AndrejChoo/USB-Programmer-parallel-flash-and-eeprom/hardware/AUTO_DCDC_MODIFICATION/AutoDCDC_MOD.jpg

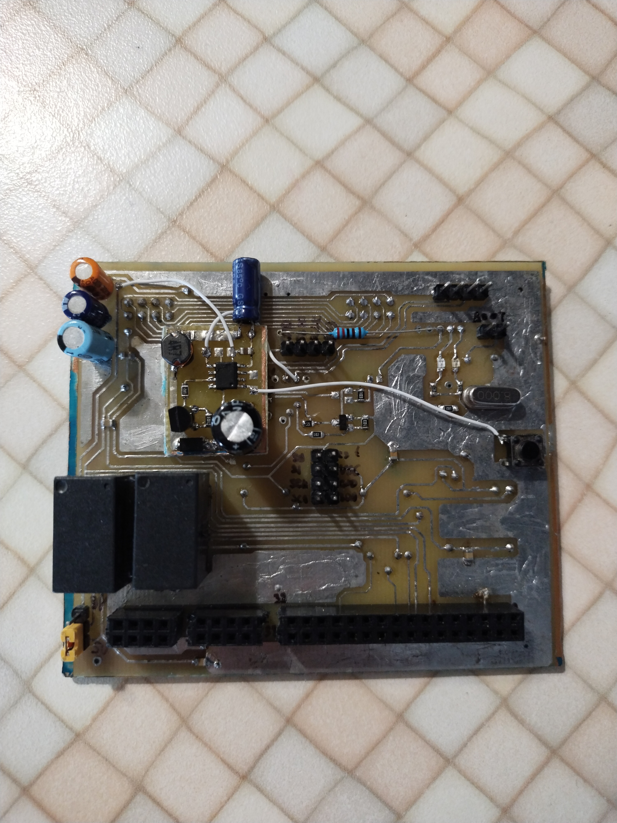
hardware/AUTO_DCDC_MODIFICATION/AutoDCDC_MOD.jpg
