AndrejChoo/USB-Programmer-parallel-flash-and-eeprom/hardware/AUTO_DCDC_MODIFICATION/PRG_SETTINGS.png

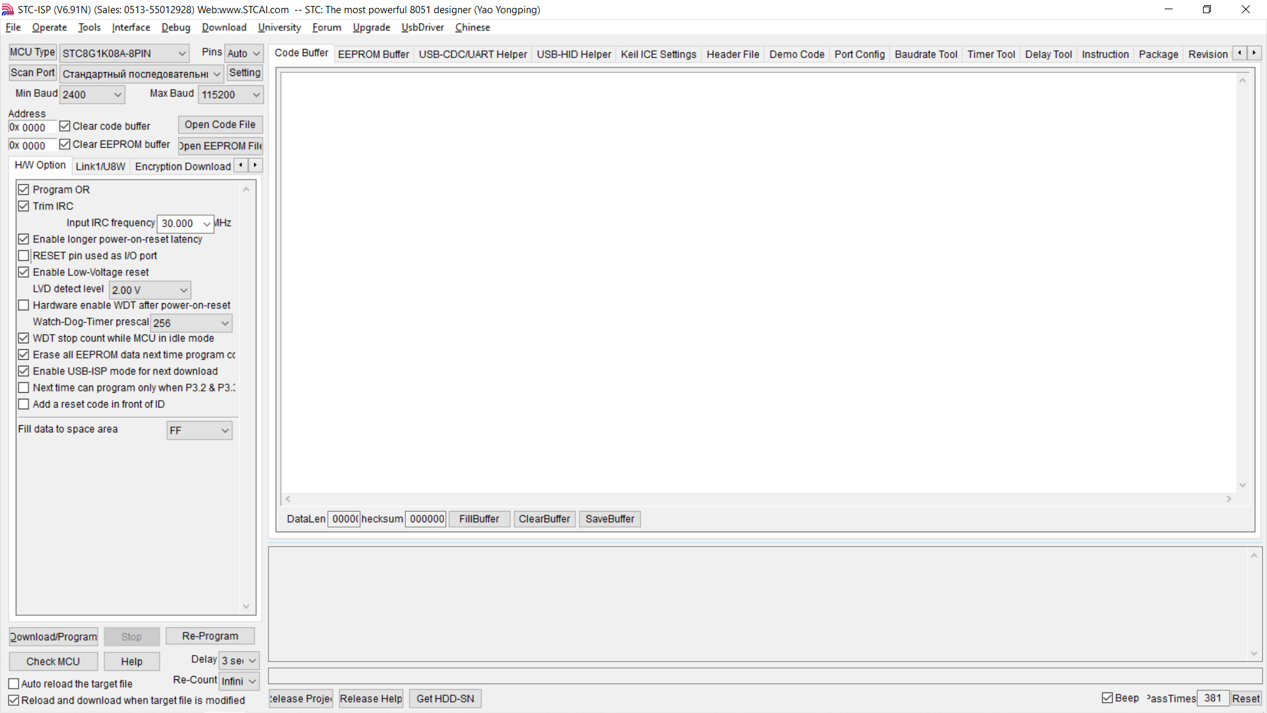
hardware/AUTO_DCDC_MODIFICATION/PRG_SETTINGS.png
