AndrejChoo/USB-Programmer-parallel-flash-and-eeprom/hardware/AUTO_DCDC_MODIFICATION/Schematic_AutoDCDC.png

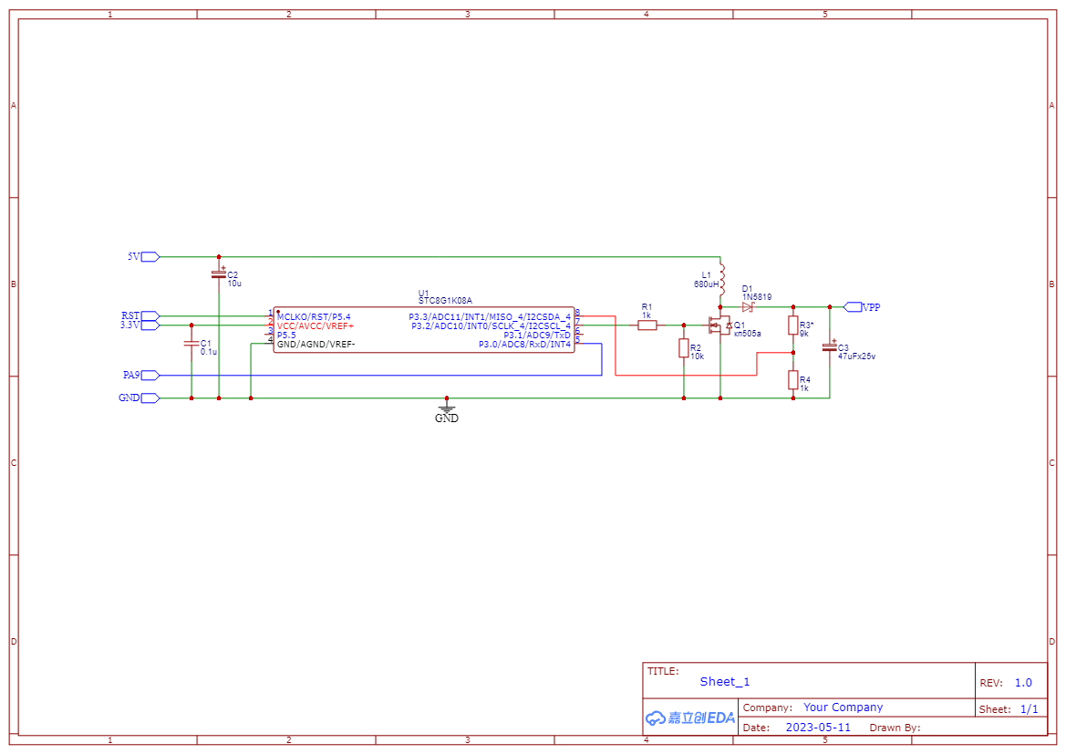
hardware/AUTO_DCDC_MODIFICATION/Schematic_AutoDCDC.png
