AndrejChoo/USB-Programmer-parallel-flash-and-eeprom/hardware/Case_model/case.jpg

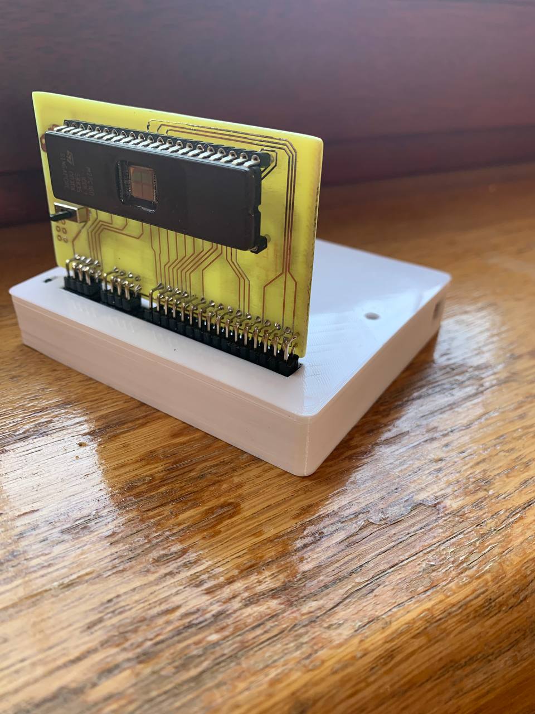
hardware/Case_model/case.jpg
