AndrejChoo/USB-Programmer-parallel-flash-and-eeprom/hardware/images/ParallelProg_v2_1_Up.jpg

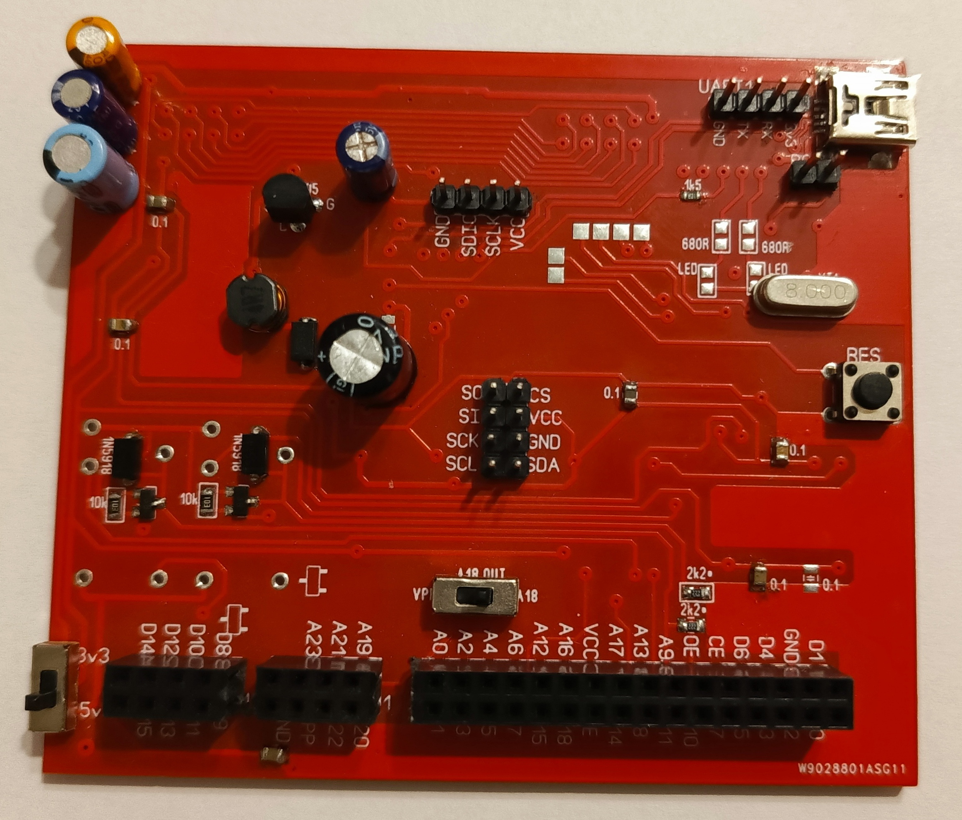
hardware/images/ParallelProg_v2_1_Up.jpg
