AndrejChoo/USB-Programmer-parallel-flash-and-eeprom/hardware/NO_RELAY_MOD/PCB_V2_NO_RELAY_PCBWAY.jpg

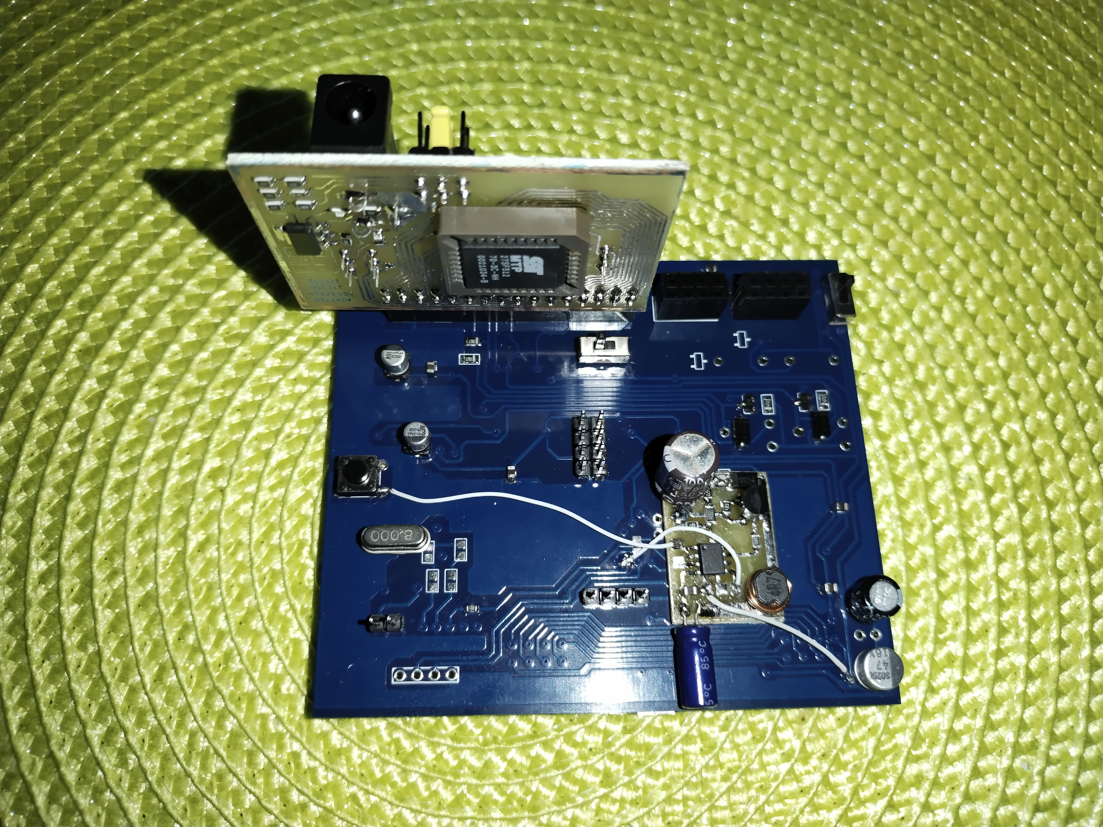
hardware/NO_RELAY_MOD/PCB_V2_NO_RELAY_PCBWAY.jpg
