AndrejChoo/USB-Programmer-parallel-flash-and-eeprom/hardware/NO_RELAY_MOD/Schematic_HV_KEY_2023-05-28.png

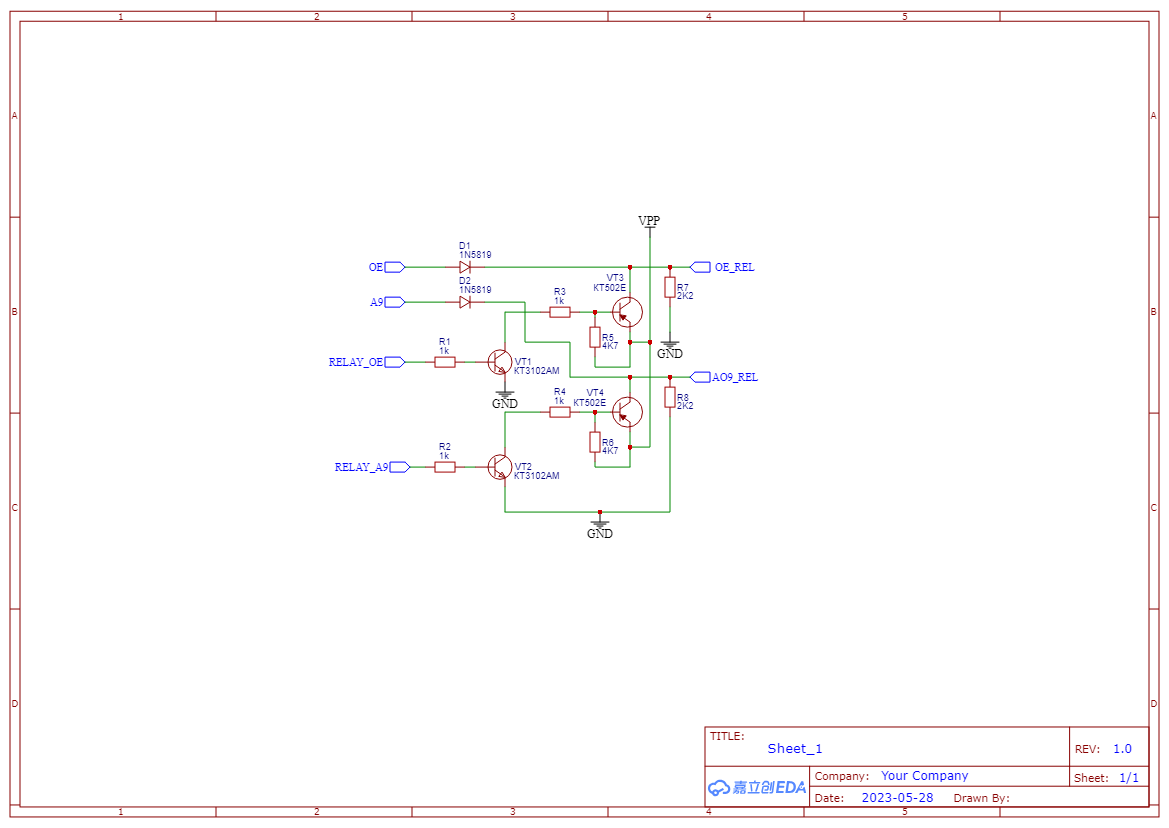
hardware/NO_RELAY_MOD/Schematic_HV_KEY_2023-05-28.png
