AndrejChoo/USB-Programmer-parallel-flash-and-eeprom/hardware/pcb/adapters/AVR/atmega_8_DIP28_Down.jpg

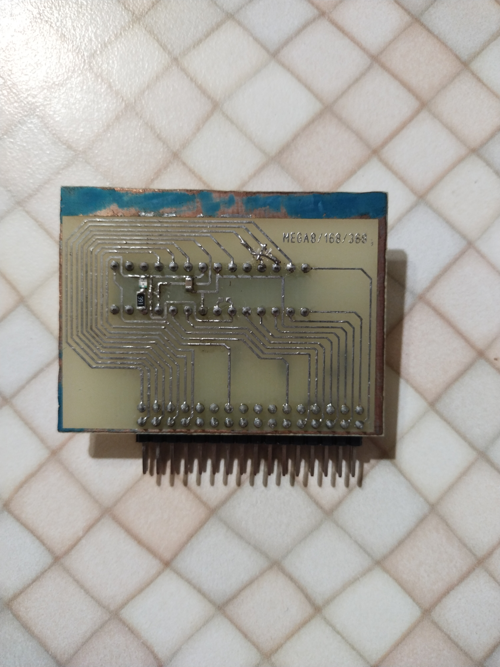
hardware/pcb/adapters/AVR/atmega_8_DIP28_Down.jpg
