AndrejChoo/USB-Programmer-parallel-flash-and-eeprom/hardware/pcb/adapters/AVR/atmega_8_DIP28_UP.jpg

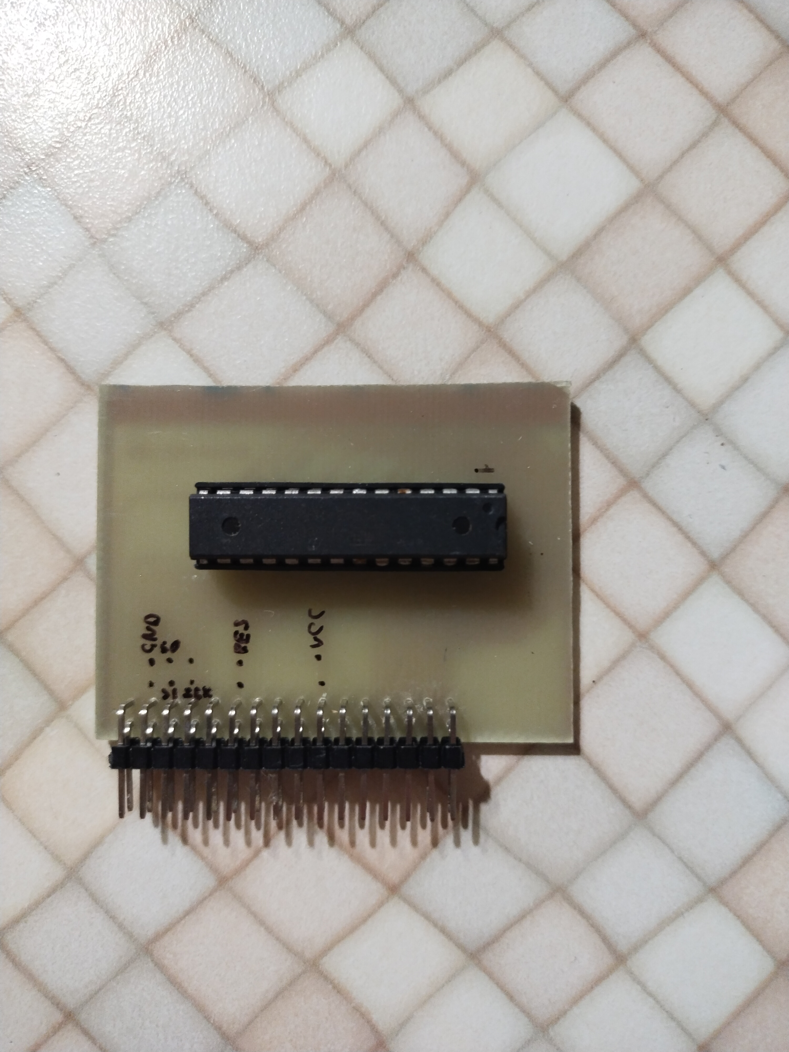
hardware/pcb/adapters/AVR/atmega_8_DIP28_UP.jpg
