AndrejChoo/USB-Programmer-parallel-flash-and-eeprom/hardware/pcb/adapters/AVR/atmega_16_DIP40_UP.jpg

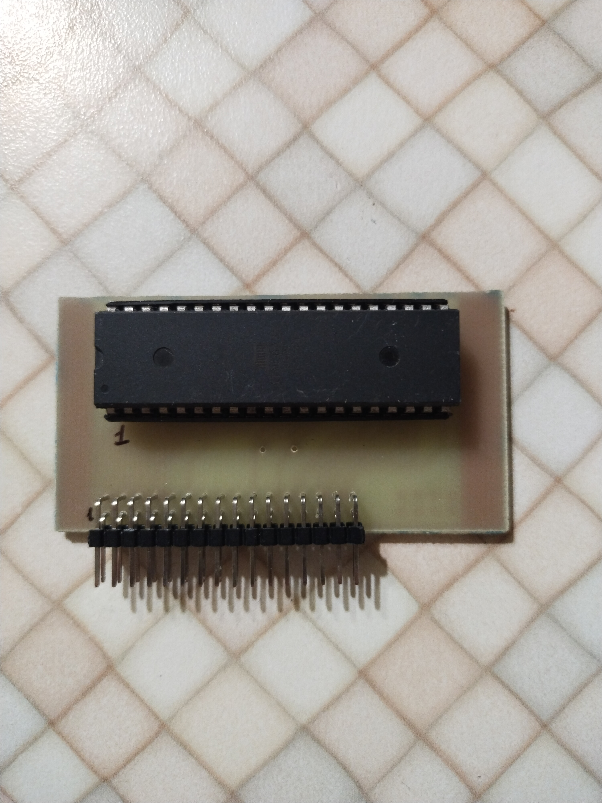
hardware/pcb/adapters/AVR/atmega_16_DIP40_UP.jpg
