AndrejChoo/USB-Programmer-parallel-flash-and-eeprom/hardware/pcb/adapters/AVR/atmega_16_DIP_40_DOWN.jpg

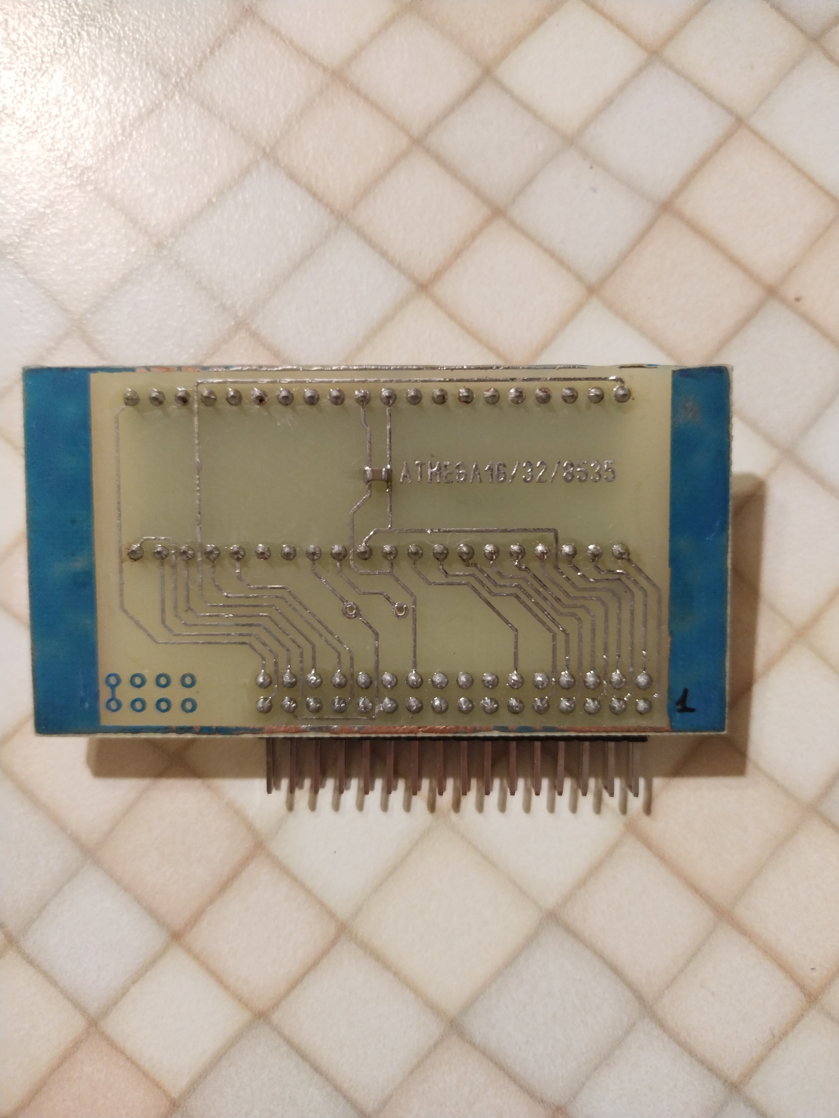
hardware/pcb/adapters/AVR/atmega_16_DIP_40_DOWN.jpg
