AndrejChoo/USB-Programmer-parallel-flash-and-eeprom/hardware/pcb/adapters/AVR/attiny_x5_UP.jpg

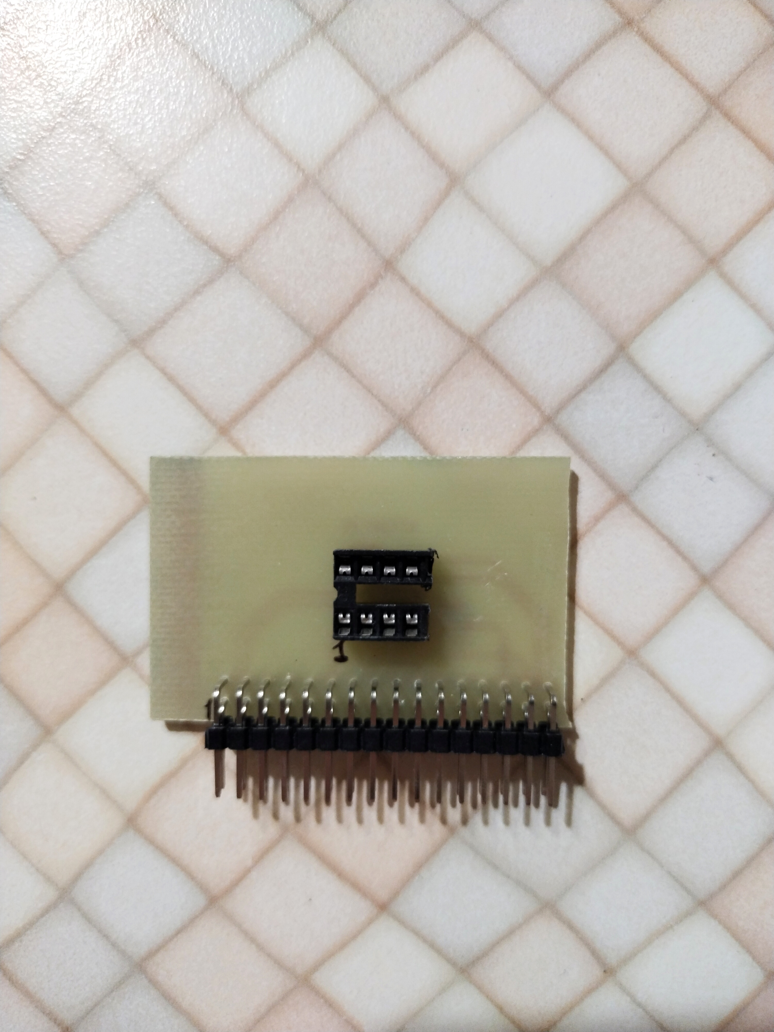
hardware/pcb/adapters/AVR/attiny_x5_UP.jpg
