AndrejChoo/USB-Programmer-parallel-flash-and-eeprom/hardware/pcb/adapters/AVR/attinyx313_DOWN.jpg

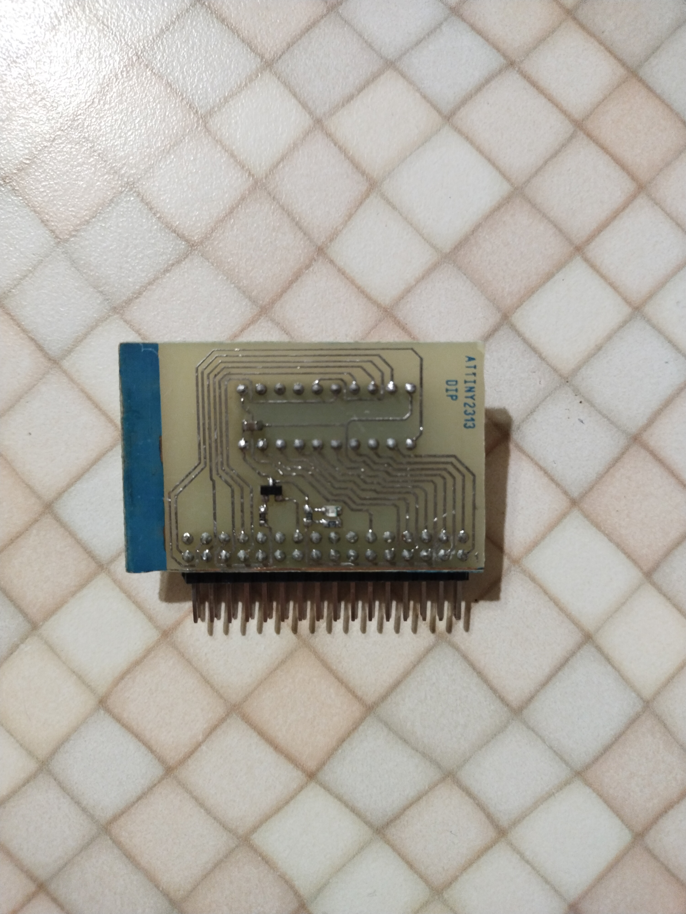
hardware/pcb/adapters/AVR/attinyx313_DOWN.jpg
