AndrejChoo/USB-Programmer-parallel-flash-and-eeprom/hardware/pcb/adapters/AVR/attynyx313_UP.jpg

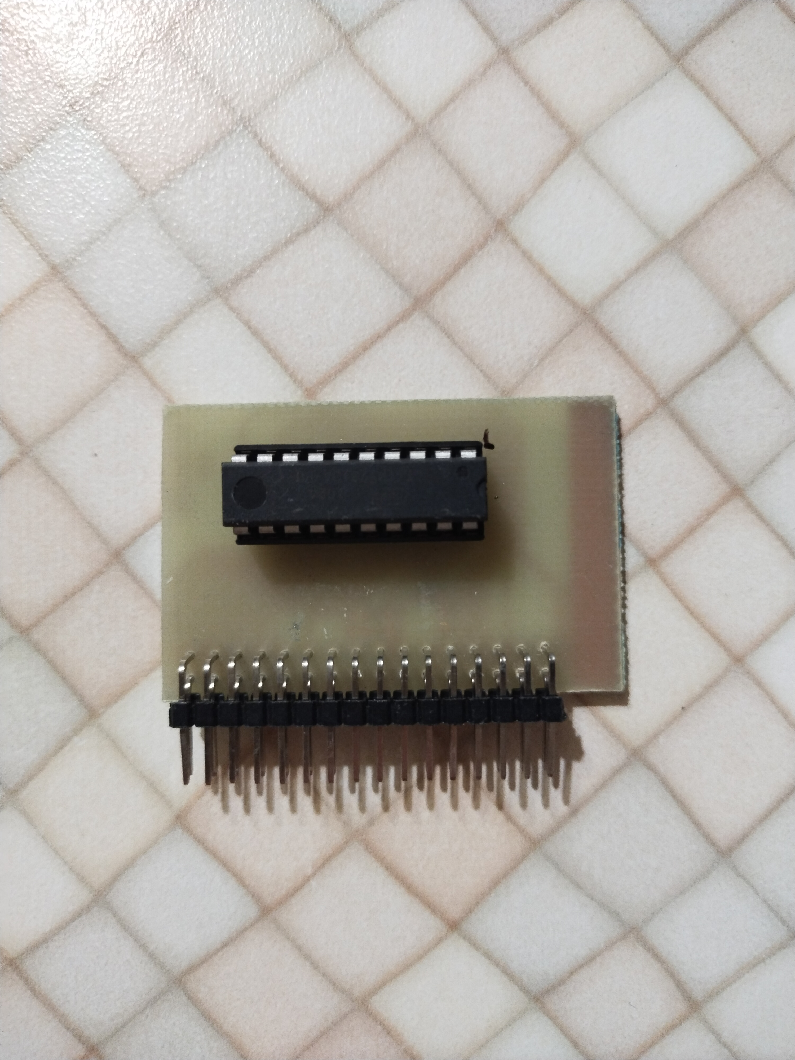
hardware/pcb/adapters/AVR/attynyx313_UP.jpg
