AndrejChoo/USB-Programmer-parallel-flash-and-eeprom/hardware/pcb/adapters/AVR/PLCC32_atmega_socket1.jpg

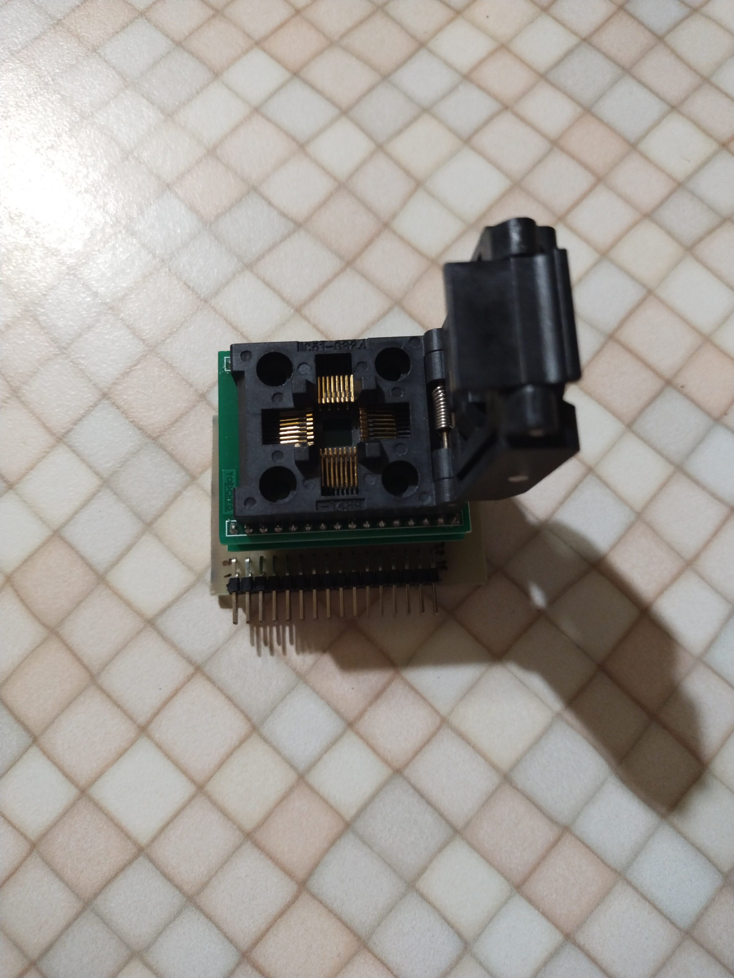
hardware/pcb/adapters/AVR/PLCC32_atmega_socket1.jpg
