AndrejChoo/USB-Programmer-parallel-flash-and-eeprom/hardware/pcb/adapters/AVR/PLCC32_atmega_socket2.jpg

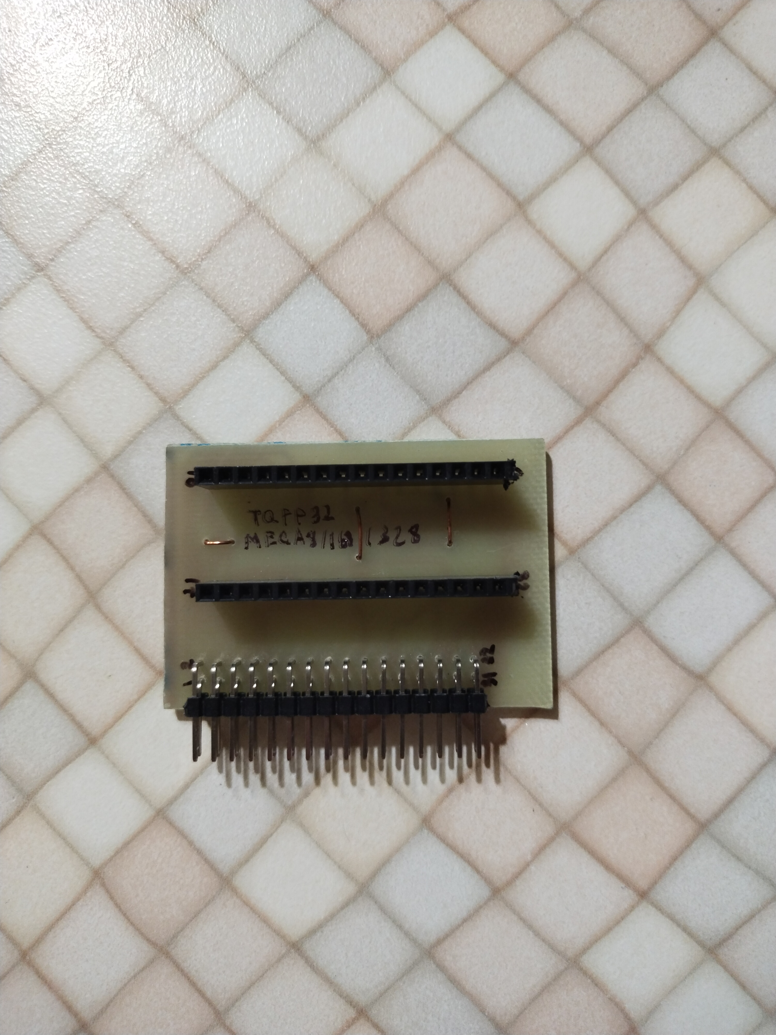
hardware/pcb/adapters/AVR/PLCC32_atmega_socket2.jpg
