AndrejChoo/USB-Programmer-parallel-flash-and-eeprom/hardware/pcb/adapters/DIP32/DOWN.jpg

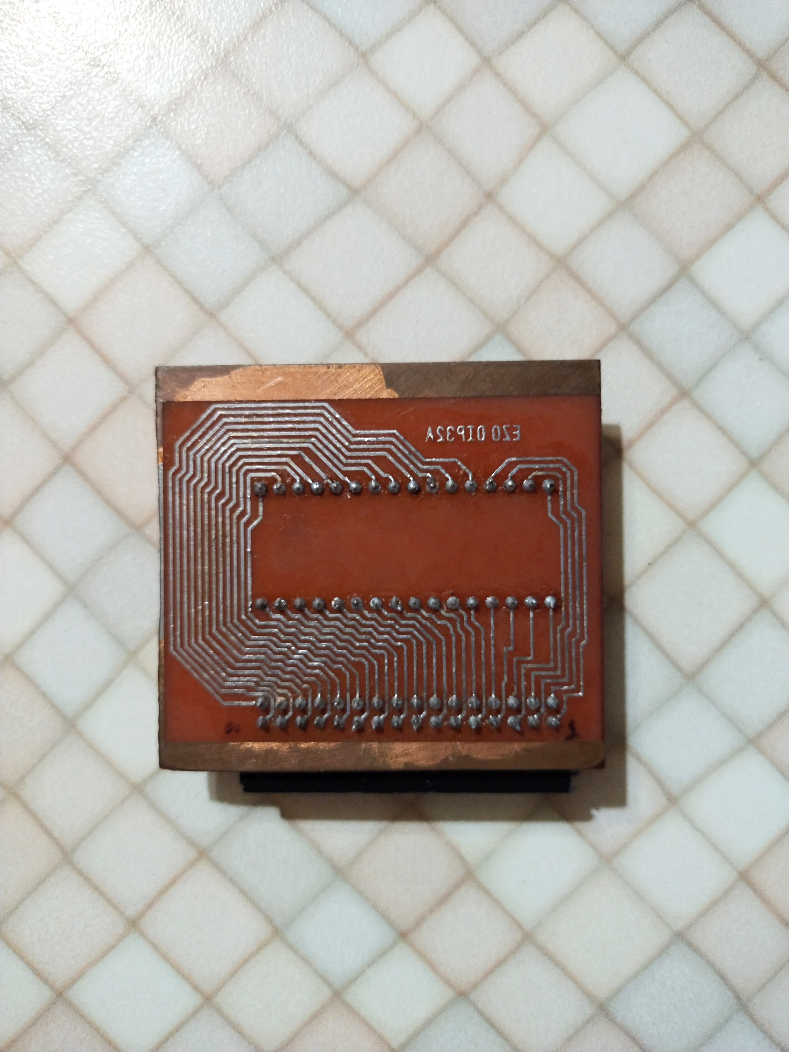
hardware/pcb/adapters/DIP32/DOWN.jpg
