AndrejChoo/USB-Programmer-parallel-flash-and-eeprom/hardware/pcb/adapters/DIP32/UP.jpg

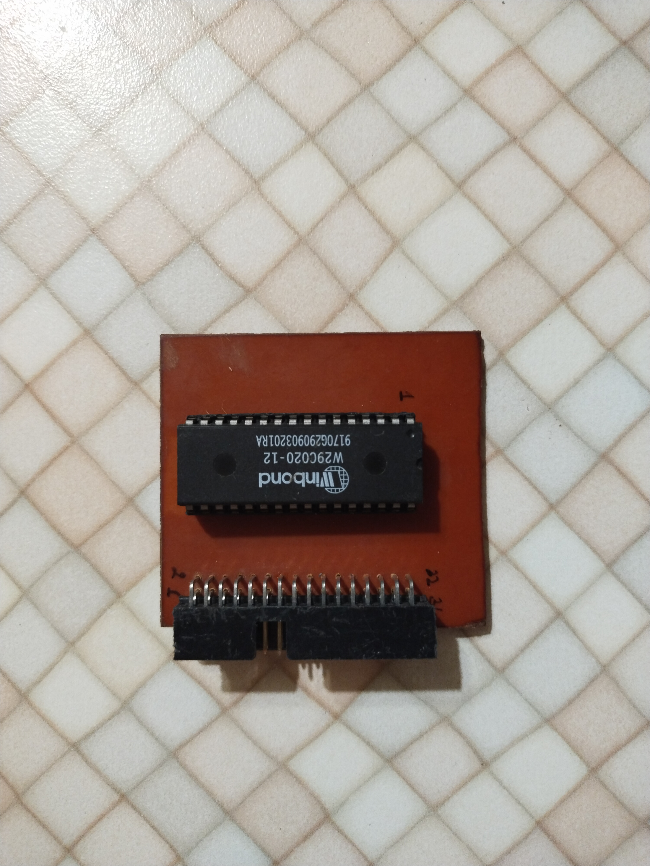
hardware/pcb/adapters/DIP32/UP.jpg
