AndrejChoo/USB-Programmer-parallel-flash-and-eeprom/hardware/pcb/adapters/EPROM_27C256_27C512/PLCC32_DOWN.jpg

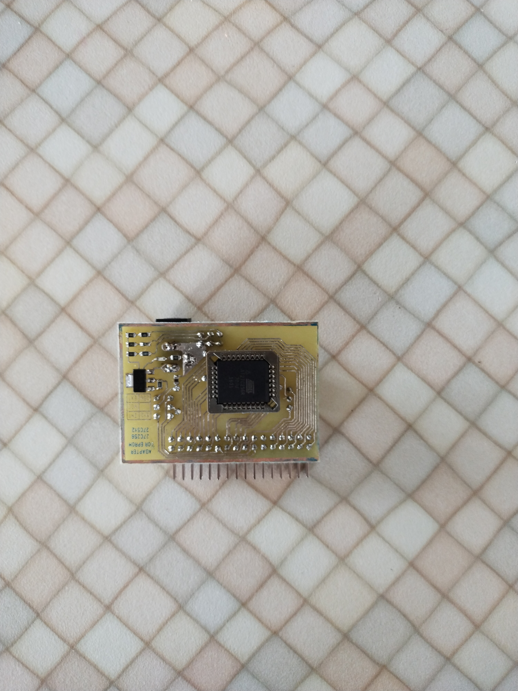
hardware/pcb/adapters/EPROM_27C256_27C512/PLCC32_DOWN.jpg
