AndrejChoo/USB-Programmer-parallel-flash-and-eeprom/hardware/pcb/adapters/EPROM_27C256_27C512/PLCC32_UP.jpg

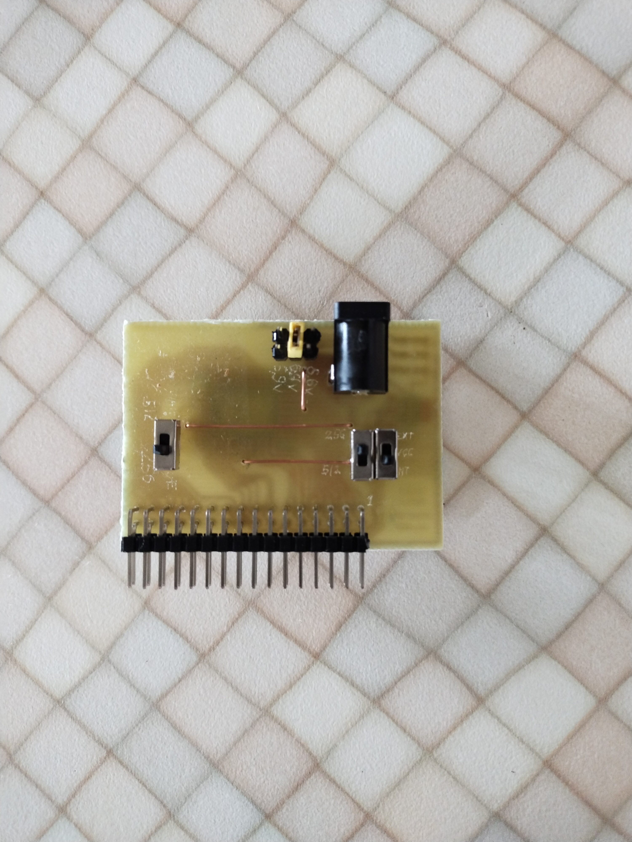
hardware/pcb/adapters/EPROM_27C256_27C512/PLCC32_UP.jpg
