AndrejChoo/USB-Programmer-parallel-flash-and-eeprom/hardware/pcb/adapters/PLCC32_HUB_FLASH/IMG_20230411_193900.jpg

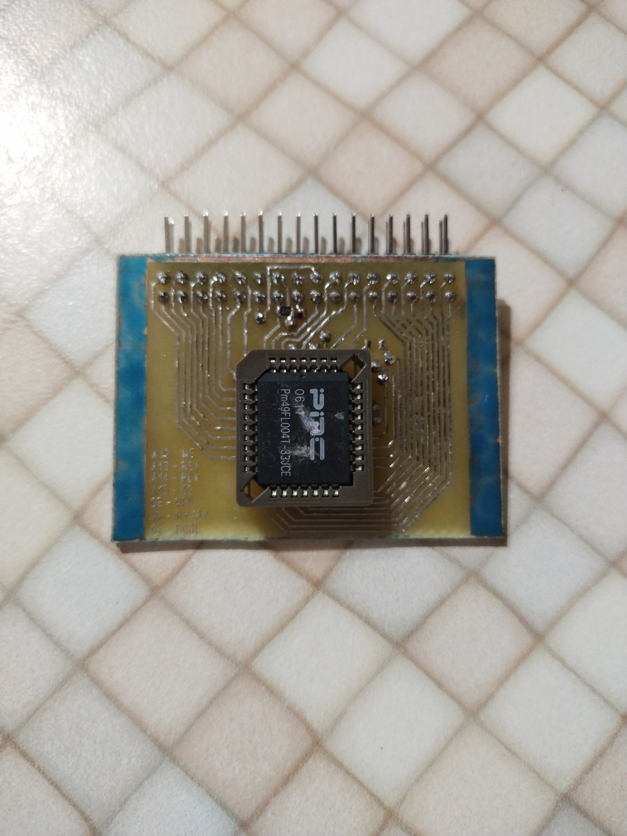
hardware/pcb/adapters/PLCC32_HUB_FLASH/IMG_20230411_193900.jpg
