AndrejChoo/USB-Programmer-parallel-flash-and-eeprom/hardware/pcb/adapters/SO28/SO28_SOCK_DOWN.jpg

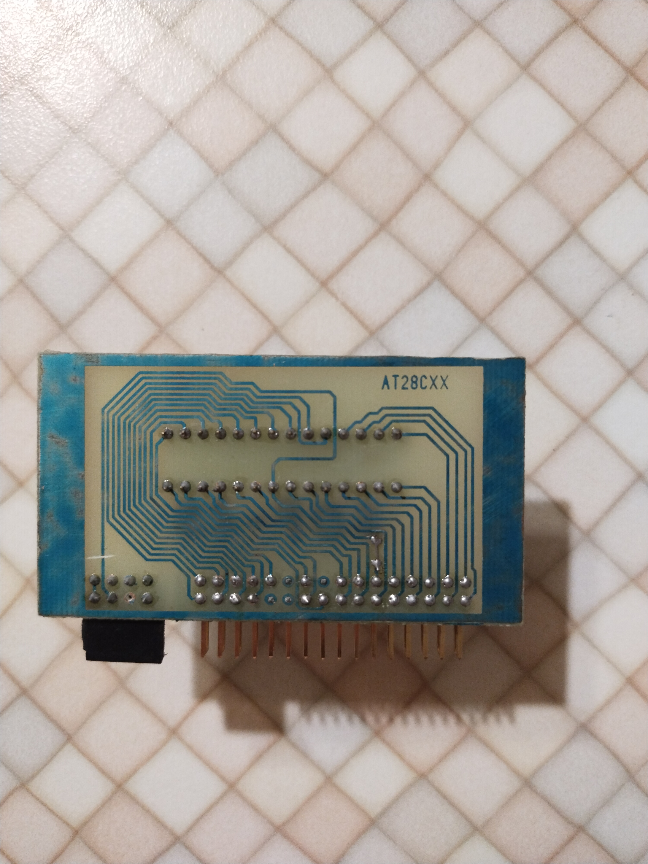
hardware/pcb/adapters/SO28/SO28_SOCK_DOWN.jpg
