AndrejChoo/USB-Programmer-parallel-flash-and-eeprom/hardware/pcb/adapters/SO28/SO28_SOCK_UP1.jpg

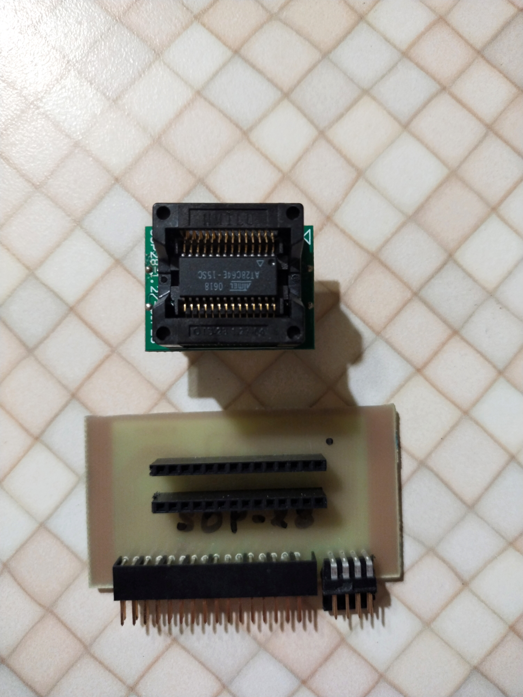
hardware/pcb/adapters/SO28/SO28_SOCK_UP1.jpg
