AndrejChoo/USB-Programmer-parallel-flash-and-eeprom/hardware/pcb/adapters/SO28/SO28_SOCK_UP.jpg

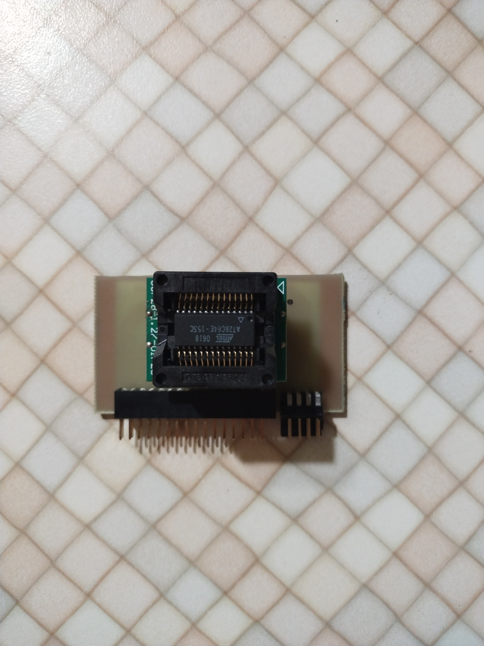
hardware/pcb/adapters/SO28/SO28_SOCK_UP.jpg
