AndrejChoo/USB-Programmer-parallel-flash-and-eeprom/hardware/pcb/adapters/TSOP32/DOWN.jpg

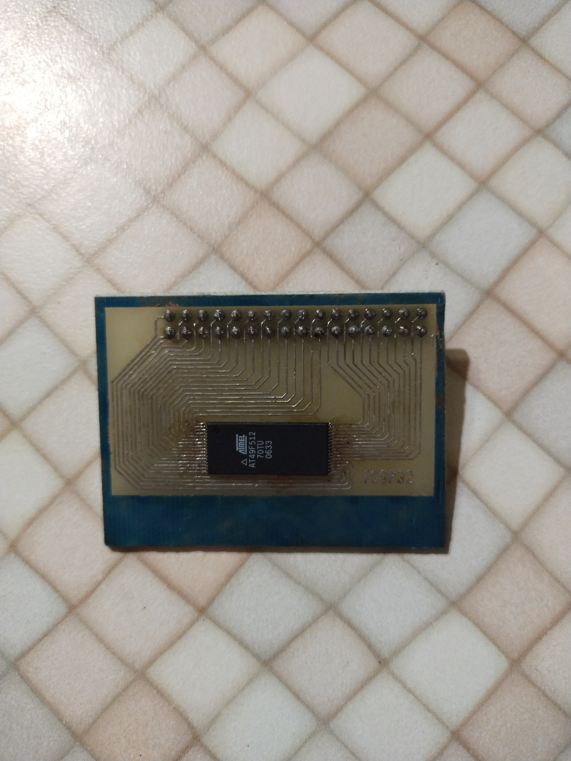
hardware/pcb/adapters/TSOP32/DOWN.jpg
