AndrejChoo/USB-Programmer-parallel-flash-and-eeprom/hardware/pcb/adapters/TSOP48_16Bit/IMG_20230411_193925.jpg

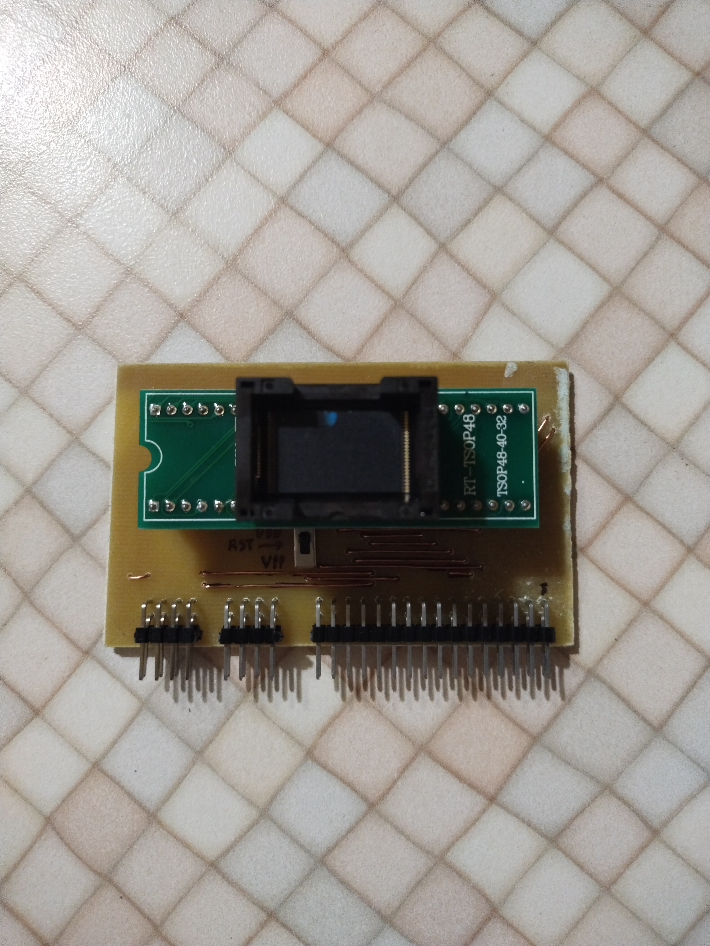
hardware/pcb/adapters/TSOP48_16Bit/IMG_20230411_193925.jpg
