AndrejChoo/USB-Programmer-parallel-flash-and-eeprom/hardware/pcb/adapters/TSOP48_16Bit/Kolodka.png

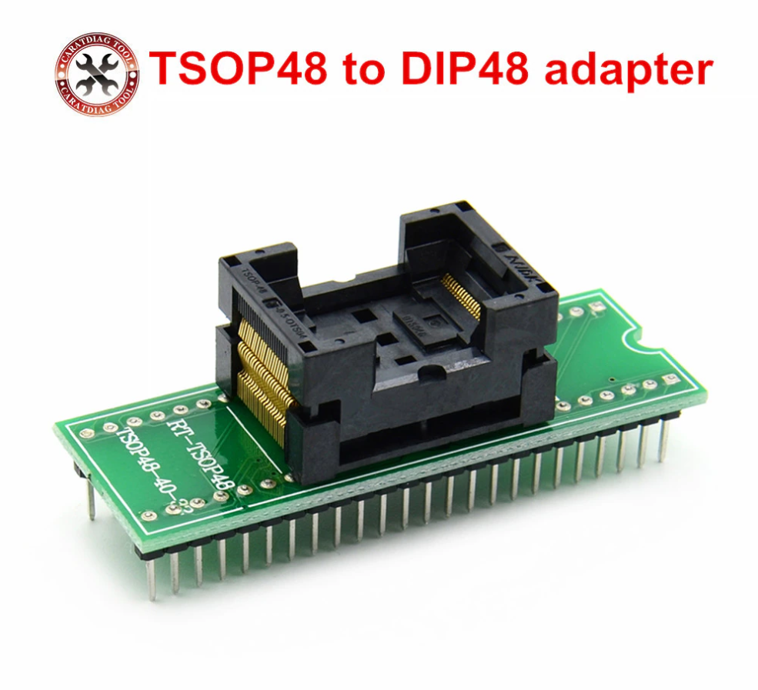
hardware/pcb/adapters/TSOP48_16Bit/Kolodka.png
