AndrejChoo/USB-Programmer-parallel-flash-and-eeprom/hardware/pcb/adapters/TSOP48_16Bit/Schematic_Flash_16b_adapter_2024-04-20.png

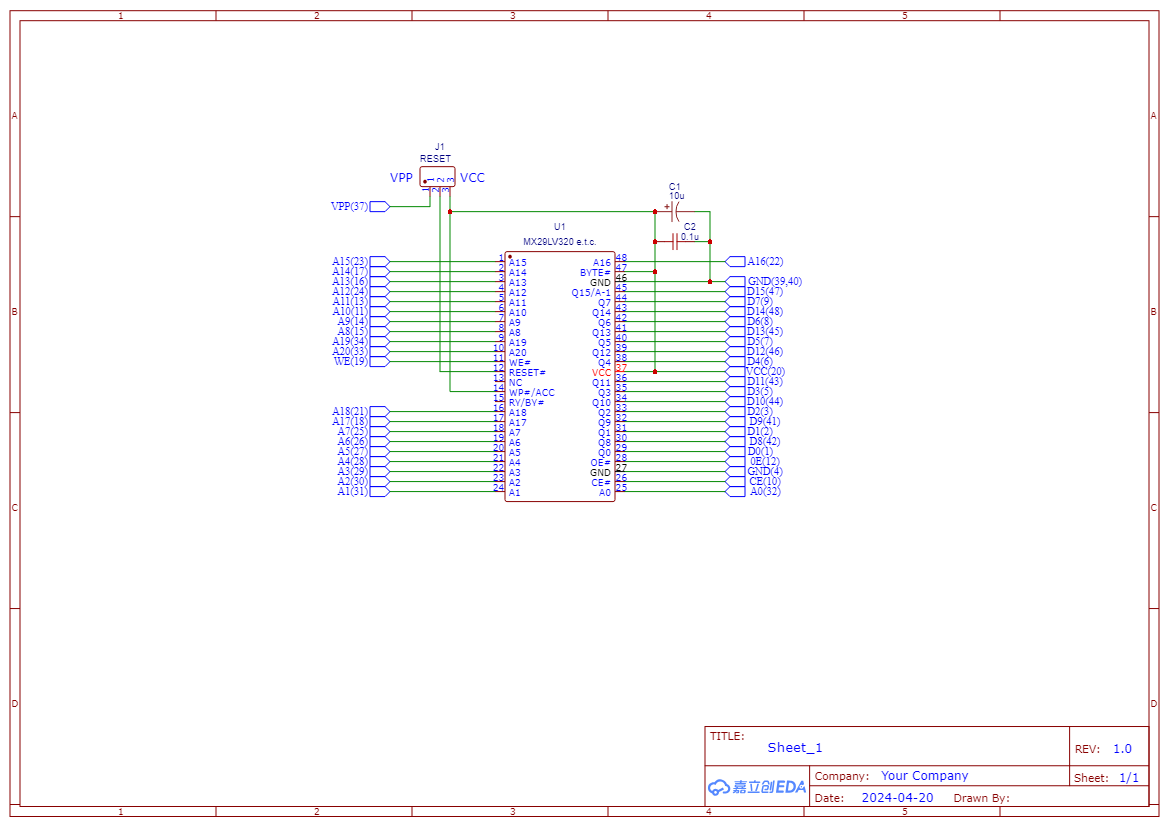
hardware/pcb/adapters/TSOP48_16Bit/Schematic_Flash_16b_adapter_2024-04-20.png
