AndrejChoo/USB-Programmer-parallel-flash-and-eeprom/hardware/AUTO_DCDC_MODIFICATION/MOD_Instruct.png

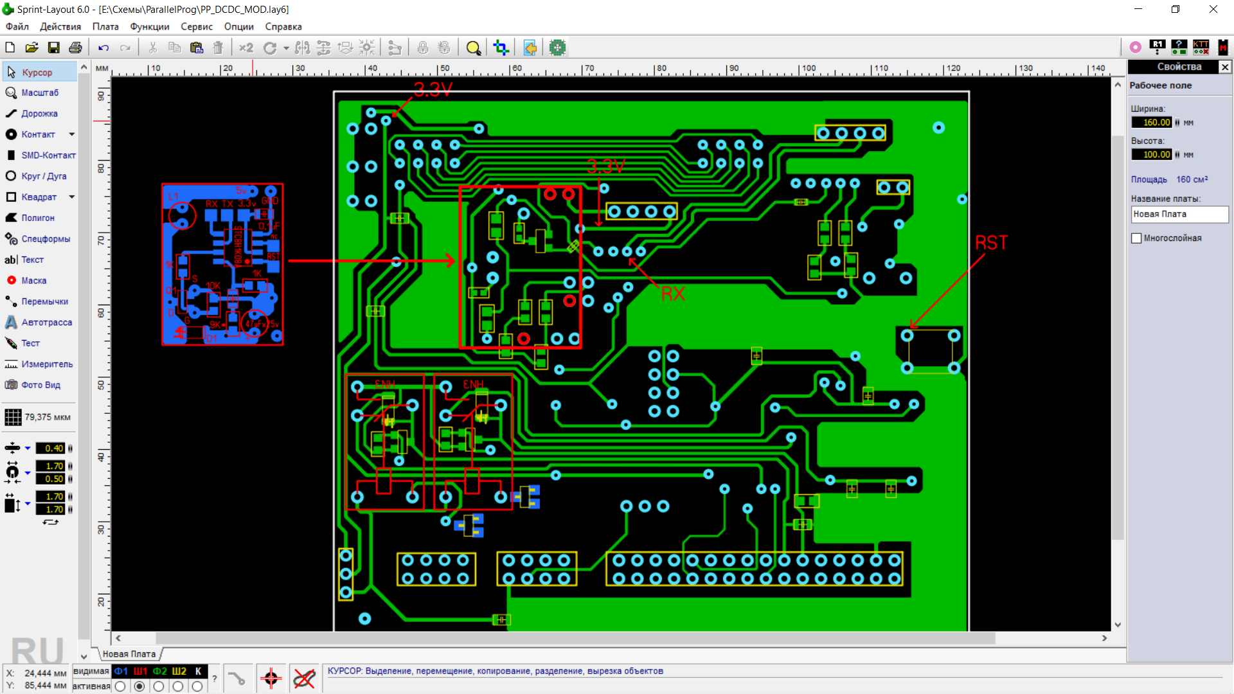
hardware/AUTO_DCDC_MODIFICATION/MOD_Instruct.png
